Pike1950/poor-mans-validation-bench/docs/modules/Module_1E_Design_Document.html

Width

# Module 1E: Function Generator / Arbitrary Waveform Generator

## Module Design Document

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

## Table of Contents

- 1. Theory of Operation
  - 1.1 Overview and signal-flow architecture
  - 1.2 Sample clock generator
  - 1.3 Address generator and waveform memory
  - 1.4 DAC stage: current-mode operation
  - 1.5 Reconstruction filter
  - 1.6 Op-amp output stage
  - 1.7 Output impedance switching
  - 1.8 Synchronization and trigger
- 2. Architectural choices
  - 2.1 Parallel data interface (vs SPI)
  - 2.2 Current-mode output (vs voltage-mode)
  - 2.3 Why AD9742 specifically
- 3. Functional figures
- 4. Schematic Notes (high-level; full schematic in KiCad)
  - DAC output stage and current-to-voltage conversion
  - Reconstruction filter
  - Op-amp differential-to-single-ended converter
  - Op-amp supply
  - Impedance switching
  - Decoupling
- 5. Pin Assignments
  - Pico 2 W parallel data + clock to AD9742
  - Pico 2 W relay control
  - Pico 2 W trigger I/O
  - Pico 2 W power
  - AD9742 pinout summary
  - AD8056 op-amp output stage
- 6. Specifications (matching SDD Table 7-27)
- 7. Sample Applications
  - 7.1 Single-tone sine generation
  - 7.2 Swept sine for THD measurement (paired with Module 2E)
  - 7.3 Multitone for IMD (intermodulation distortion)
  - 7.4 White noise for noise-floor characterization
  - 7.5 Clock generation for digital characterization
  - 7.6 Bias-mode voltage injection
- 8. Bill of Materials
- 9. Calibration Procedure
  - 9.1 DC offset calibration
  - 9.2 Gain calibration
  - 9.3 Frequency calibration
  - 9.4 Reconstruction filter passband flatness
- 10. Bring-Up Checklist
- 11. Known Issues and Future Work
- 12. References

## 1. Theory of Operation

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

### 1.1 Overview and signal-flow architecture

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

Figure 1E-1: Module 1E AWG functional architecture

Module 1E AWG functional architecture: textbook AWG blocks mapped to the Pico + AD9742 + AD8056 realization

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

### 1.2 Sample clock generator

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

Two clock-accuracy modes are available:

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

### 1.3 Address generator and waveform memory

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

Figure 1E-2: Phase accumulator (textbook DDS view)

Phase accumulator: FTW register feeds an adder whose output latches into the Phase register, clocked by f_CLK, with the Phase register output feeding back to the adder via a 32-bit bus. Top 10 bits 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

### 1.4 DAC stage: current-mode operation

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

Figure 1E-3: AD9742 current-mode DAC operation (simplified)

Conceptual view of AD9742 current-mode operation: PMOS source array, code-driven switching to IOUTA/IOUTB, load resistors and FSADJ

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

Four parameters set the operating point:

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

### 1.5 Reconstruction filter

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

Two phenomena combine to create the output spectrum:

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

Figure 1E-4: DAC output spectrum at 50 MSPS burst-rate (best case)

DAC output spectrum at 50 MSPS burst rate: baseband at 10 MHz, first image at 40 MHz attenuated by ~52 dB after the 5th-order Butterworth

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

Figure 1E-5: DAC output spectrum at 30 MSPS sustained-rate floor (worst case)

DAC output spectrum at 30 MSPS sustained rate: baseband at 10 MHz, first image now at 20 MHz attenuated by only ~22 dB, ZOH sinc droops harder

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

Figure 1E-6: Reconstruction filter response, singly- vs doubly-terminated design

Reconstruction filter magnitude response: three 5th-order Butterworth designs in the same 25 ohm source / 1 kohm load circuit. The two doubly-terminated designs (50 ohm and 158 ohm) ripple 6 to 11 d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

### 1.6 Op-amp output stage

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

The difference-amp topology is the classic four-resistor configuration:

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

### 1.7 Output impedance switching

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

### 1.8 Synchronization and trigger

Two GPIOs on the Pico expose the module's relationship with the chassis trigger bus:

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

## 2. Architectural choices

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

### 2.1 Parallel data interface (vs SPI)

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

### 2.2 Current-mode output (vs voltage-mode)

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

Four reasons current-mode is the standard for AWG-class parts:

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

### 2.3 Why AD9742 specifically

Within the 12-bit, ~200 MSPS, parallel current-output category, the AD9742 won on three axes:

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

## 3. Functional figures

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

Figure 1E-7: AD9742 internal functional block diagram

AD9742 internal block diagram, redrawn from datasheet Rev. C

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

Figure 1E-8: Module 1E typical application schematic

Pico 2 W → AD9742 → reconstruction filter → AD8056 → 50/high-Z/10kΩ relay → BNC

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

## 4. Schematic Notes (high-level; full schematic in KiCad)

### DAC output stage and current-to-voltage conversion

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

### Reconstruction filter

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

### Op-amp differential-to-single-ended converter

The AD8056 channel A is configured as a difference amplifier:

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

### Op-amp supply

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

### Impedance switching

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

### Decoupling

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

## 5. Pin Assignments

### Pico 2 W parallel data + clock to AD9742

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

### Pico 2 W relay control

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

Firmware enforces mutually exclusive relay energizing.

### Pico 2 W trigger I/O

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

### Pico 2 W power

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

### AD9742 pinout summary

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

### AD8056 op-amp output stage

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

## 6. Specifications (matching SDD Table 7-27)

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

## 7. Sample Applications

### 7.1 Single-tone sine generation

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

### 7.2 Swept sine for THD measurement (paired with Module 2E)

import numpy as np
from scipy.fft import rfft, rfftfreq

awg = open_module('1E')
scope = open_module('2E')

awg.write('OUTP:IMP 50')
frequencies = np.logspace(np.log10(20), np.log10(20000), 31)
results = []

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

for f, thd in results:
    print(f'{f:8.1f} Hz: THD = {thd*100:.3f}%')

### 7.3 Multitone for IMD (intermodulation distortion)

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

### 7.4 White noise for noise-floor characterization

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

### 7.5 Clock generation for digital characterization

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

### 7.6 Bias-mode voltage injection

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

## 8. Bill of Materials

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

## 9. Calibration Procedure

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

### 9.1 DC offset calibration

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

### 9.2 Gain calibration

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

### 9.3 Frequency calibration

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

### 9.4 Reconstruction filter passband flatness

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

## 10. Bring-Up Checklist

In order, on first power-up:

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

## 11. Known Issues and Future Work

(To be populated as the module is built.)

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

## 12. References

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
