Pike1950/poor-mans-validation-bench/docs/chassis/Chassis_Architecture_and_Power_Distribution.html

# Chassis Architecture and Power Distribution Design Document

## v1.0 (May 2026)

Companion to the PMVB System Design Document section 11. This document defines the mechanical and electrical design of the PMVB chassis: an open-frame card-cage acrylic enclosure (4 panels laser-cut from SendCutSend, clamped by 4 M3 corner standoffs) housing the Silverstone SST-TX300 PSU as an analog-rail backbone, a GeeekPi D-1188 ATX breakout, a Sabrent HB-BU10 USB 3.0 hub as the chassis-internal USB-TMC backplane, and 14 module slots arranged as parallel vertical blades.

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

v1.0 is open-frame. The chassis has a floor, a ceiling, and two internal divider plates (the bottom and top groove plates with the module-slot through-cuts), but no side walls, rear wall, or front panel. Walls were dropped because the four corner standoffs handle structural rigidity on their own, and adding walls re-introduces TX300 thermal-management constraints (intake/exhaust airflow, vent geometry) that warrant their own design pass. The walled chassis with explicit ventilation geometry is the v1.1 future enhancement described in section 9. Until then, the bench operator gets unrestricted visual and physical access to all chassis internals — TX300, GeeekPi breakout, USB hub, harness, and modules — from any side.



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

## Table of Contents

- 1. Design Philosophy
- 2. Functional Block Diagram
- 3. Mechanical Architecture
  - 3.1 Outer Envelope and Form Factor
  - 3.2 Acrylic Frame and Cuts
  - 3.3 TX300 PSU Mounting
  - 3.4 GeeekPi D-1188 Mounting
  - 3.5 Sabrent HB-BU10 USB Hub Mounting
  - 3.6 Module Slot Geometry and Form Factor
  - 3.7 Diagnostic Strip (deferred to v1.1)
  - 3.8 TX300 Fan Ventilation (v1.0 open-frame)
- 4. Electrical Architecture
  - 4.1 Rail Sources from the TX300
  - 4.2 GeeekPi D-1188 ATX Breakout
  - 4.3 Per-Rail Fuse Panel
  - 4.4 4-Wire Back-Wall Harness
  - 4.5 Per-Module Phoenix Pigtail
  - 4.6 Banana-Jack Diagnostic Test Points
  - 4.7 Front-Panel Indicator LEDs
- 5. USB-TMC Backplane
- 6. Bill of Materials
- 7. Bring-Up Procedure
- 8. Safety Procedures
- 9. Future Enhancements
- 10. References

## 1. Design Philosophy

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

## 2. Functional Block Diagram



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

## 3. Mechanical Architecture

### 3.1 Outer Envelope and Form Factor

The v1.0 chassis is an open-frame card cage with envelope dimensions 435 × 238 × 92 mm (~17.1" × 9.4" × 3.6"). Material is 3 mm cast acrylic throughout, laser-cut from SendCutSend with the parts list described in section 3.2. The bench footprint is comparable to a 1U–2U rack-mount instrument.

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

### 3.2 Acrylic Frame and Cuts

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

Groove plate (bottom and top divider)

435 × 238 × 3

2

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

### 3.3 TX300 PSU Mounting

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

### 3.4 GeeekPi D-1188 Mounting

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

These holes are cut as 2.7 mm clearance holes (M2.5 normal clearance) in both the ceiling plate and the top groove plate (see section 3.2 for the panel detail). The GeeekPi's own mounting holes are 2.5 mm and accept M2.5 screws directly (no drill-out needed).

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

### 3.5 Sabrent HB-BU10 USB Hub Mounting

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

### 3.6 Module Slot Geometry and Form Factor

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

Connector positions on the host PCB:

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

### 3.7 Diagnostic Strip (deferred to v1.1)

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

### 3.8 TX300 Fan Ventilation (v1.0 open-frame)

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

## 4. Electrical Architecture

### 4.1 Rail Sources from the TX300

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

### 4.2 GeeekPi D-1188 ATX Breakout

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

### 4.3 Per-Rail Fuse Panel

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

Fuse selection details:

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

### 4.4 4-Wire Back-Wall Harness

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

### 4.5 Per-Module Phoenix Pigtail

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

### 4.6 Banana-Jack Diagnostic Test Points (deferred to v1.1)

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

### 4.7 Front-Panel Indicator LEDs (deferred to v1.1)

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

## 5. USB-TMC Backplane

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

## 6. Bill of Materials

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

## 7. Bring-Up Procedure

In order on first power-up, before any module is installed:

### 7.1 Mechanical assembly verification

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

### 7.2 Electrical bring-up, no modules

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

### 7.3 Back-wall harness bring-up

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

### 7.4 USB hub bring-up

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

### 7.5 First-module bring-up

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

### 7.6 Full population

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

## 8. Safety Procedures

### 8.1 Daily operation

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

### 8.2 Working inside the chassis

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

### 8.3 Shared work / lockout-tagout

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

This is overkill for solo hobbyist work but matches industry practice and is worth practicing.

## 9. Future Enhancements

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

### 9.1 v1.1 walled chassis with explicit ventilation geometry

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

### 9.2 Front panel with per-module faceplate cutouts and diagnostic strip

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

### 9.3 Custom 4-rail distribution PCB

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

### 9.4 v2.0 chassis form factor

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

### 9.5 Chassis LAN switch

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

## 10. References

- PMVB System Design Document - canonical architecture and module catalog.
- Module 1E Design Document - first module to fully populate, drives the chassis bring-up.
- Silverstone TX300 datasheet (300 W TFX 80+ Bronze).
- GeeekPi D-1188 ATX 24-pin breakout product page (Amazon B08MC389FQ).
- Sabrent HB-BU10 USB 3.0 10-port hub product page (Amazon B0797NZFYP).
- SendCutSend laser-cut acrylic service: dimensional rules and material datasheet.
- JLCPCB FDM 3D printing service: design rules for module body fabrication.
- Wago 221-413 datasheet: 3-conductor compact splicing connector, 12-24 AWG.
- Phoenix Contact MC 1,5/4-G-3,81 and MC 1,5/4-ST-3,81 datasheets: pluggable PCB header and cable plug pair.
