Pike1950/poor-mans-validation-bench/docs/figures/modules/1e_ad9742_internal.tex

% =============================================================================
% Figure 1E-2: AD9742 internal functional block diagram
% =============================================================================
% Embeds the official Analog Devices block diagram from the AD9742 datasheet
% (Rev. C, page 1).
%
% The image must live at the path referenced below. By default it expects
% the public-facing copy under docs/figures/modules/external/, NOT the
% gitignored Reference Photos/ folder, so that GitHub Pages can render it.
%
% Image source workflow (already done; documented for reproducibility):
%   mkdir -p docs/figures/modules/external
%   cp "Reference Photos/ICs/AD9742/AD9742-fbl.png" \
%      docs/figures/modules/external/ad9742_datasheet_block_diagram.png
%
% Compile:  pdflatex 1e_ad9742_internal.tex
% Convert:  pdftocairo -svg 1e_ad9742_internal.pdf
% =============================================================================
\documentclass[border=8pt]{standalone}
%
\input{../style/pmvb-figures.sty}
\usepackage{graphicx}
%
\begin{document}
\begin{tikzpicture}[pmvb figure]
  %
  % --- Embedded datasheet figure ------------------------------------------
  % Width set to 180mm so the rendered SVG carries enough intrinsic size
  % to read clearly when scaled to width:100% in the design doc HTML.
  \node (img) at (0, 0)
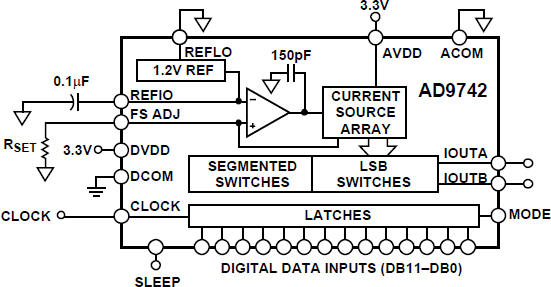
[picture p8: docs/figures/modules/external/ad9742_datasheet_block_diagram.png]
    {};
  %
  % Caption and attribution are rendered in the design doc, not embedded
  % in the SVG.
\end{tikzpicture}
\end{document}
