Pike1950/poor-mans-validation-bench/tools/fabrication/out/chassis_assembly_exploded.png

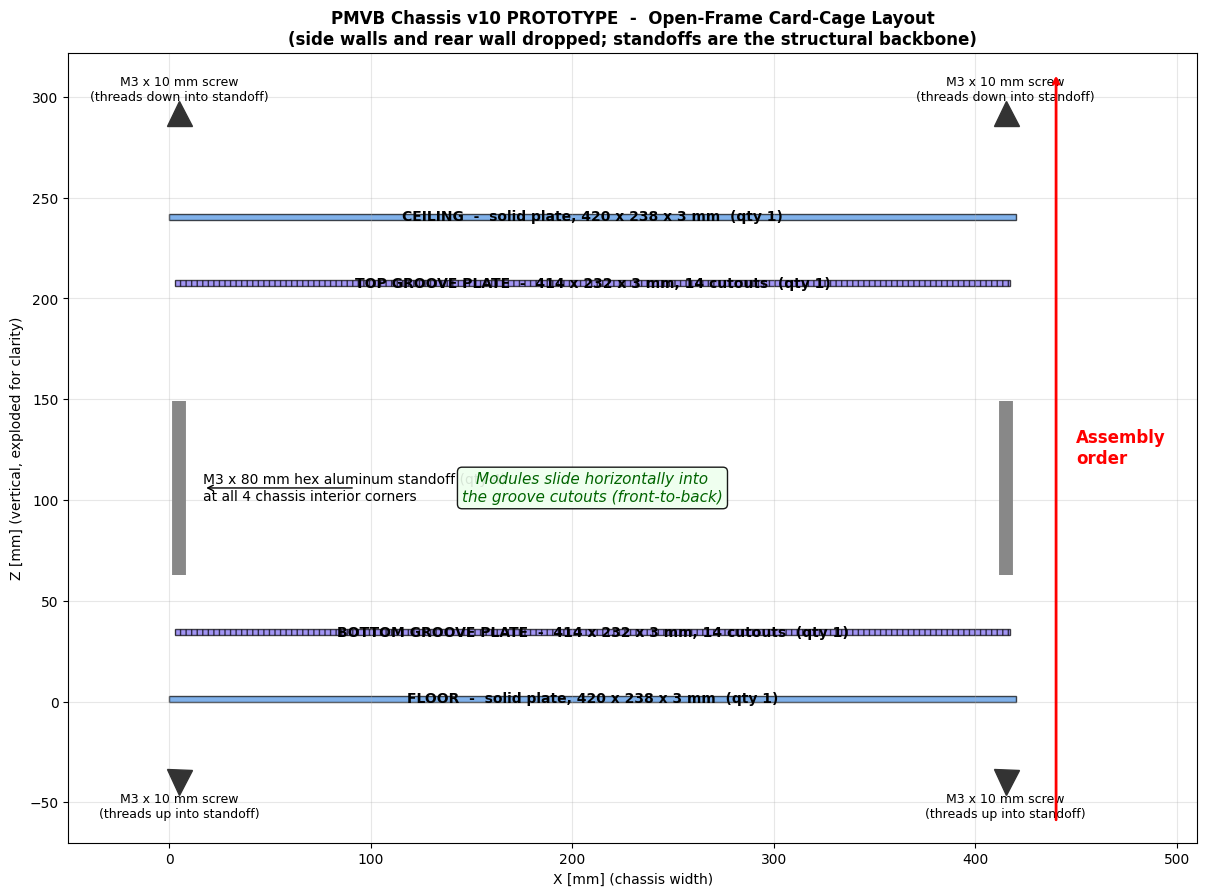
tools/fabrication/out/chassis_assembly_exploded.png
