Pike1950/poor-mans-validation-bench/tools/fabrication/out/panel_groove_plate_preview.png

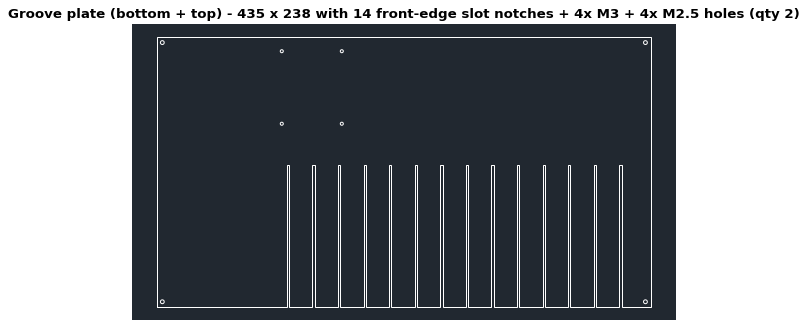
tools/fabrication/out/panel_groove_plate_preview.png
